bebenlebricolo/NanoFridgeThermostat/Hardware/Simulations/ACCurrentSensingAmp1.asc

C1: cap; 100n
C2: cap; 1µ
C3: cap; 1µ
C4: cap; 1µ
R1: res; 22k
R2: res; 10k
R3: res; 100k
R4: res; 56k
R5: res; 100k
R6: res; 100k
R7: res; 100k
R8: res; 10k
U1: TL072
U2: TL072
V1: signal; SINE(0 5m 50 0 0 0 2000)
V2: signal; SINE(0 2m 10000 0 0 0 2000)
V3: voltage; 5
Named nets: 0, VoutStage1, Filtered, Vin, Pol, Vcc, Vout
.tran 0 0.2 0
Dual stage TL072 JFet input op amp.
This configuration filters input AC current to select 50/60Hz main current
and feeds a 2 stages amplifier configuration.
Input amplitude (peak-to-peak) is around 5mV @50Hz
Output amplitude is about 180mV. 
Overall gain is around 36.
