bebenlebricolo/NanoFridgeThermostat/Firmware/src/Core/led.c

#include <stdbool.h>
#include <stddef.h>
#include <string.h>

#include "interpolation.h"
#include "led.h"

#ifdef LED_PWM_PULSE_STUFFING
#include "spanner.h"
#endif

typedef struct
{
    bool configured;           /**> Used to know if this specific LED construct is used or not      */
    led_io_t io;               /**> Static led IO config                                            */
    uint8_t io_state;          /**> IO state, only used for the LED_BLINK_NONE pattern (aka SOLID)  */
    mcu_time_t last_processed; /**> Last time this LED was processed (used to perform soft PWM)     */
    struct
    {
        led_blink_pattern_t current;  /**> Current LED Pattern (used to trigger state changed events)                                       */
        led_blink_pattern_t previous; /**> Previous LED Pattern (used to trigger state changed events)                                      */
    } patterns;

    led_next_event_t event; /**> Event that'll be triggered when the LED pattern is finished processing (some of the patterns have a limited life)  */

    struct
    {

        /**
         * @brief breathing LED pattern configuration and trackers
         */
        struct
        {
            uint16_t step;   /**> Keeps track of the current duty cycle applied to the LED   */
            bool new_step;   /**> Used to trigger the "new step" event. Some computation is performed only once to save time */
            uint8_t on_time; /**> Currently applied duty cycle : 0 - 100                                                     */

#ifdef LED_PWM_PULSE_STUFFING
            struct
            {
                bool used;     /**> Tells the algorithm whether stuffing is currently in use or not                   */
                uint8_t index; /**> Current index in the data sequence                                                */
                uint8_t sequence[LED_BLINK_BREATHING_RESOLUTION_MS]; /**> Sequence spans over max Resolution (for 100Hz signal with millisecond tick,
                                                                        resolution is 10). This field is used when the desired duty cycle can't be
                                                                        exactly represented with the physical resolution, hence pulse stuffing needs
                                                                        to be applied */

            } stuffing;
#endif /* LED_PWM_PULSE_STUFFING */
        } breathing;

        struct
        {
            uint8_t count; /**> Keeps track of the amount of blinks already executed       */
        } accept;
    } states;
} internal_config_t;

static internal_config_t internal_config[MAX_LED_COUNT];

static void handle_led_accept(mcu_time_t const *const time, internal_config_t *const config);
static void handle_led_warning(mcu_time_t const *const time, internal_config_t *const config);
static void handle_led_breathing(mcu_time_t const *const time, internal_config_t *const config);
static void get_elapsed_milliseconds(mcu_time_t const *const time, internal_config_t *const config, uint32_t *const elapsed);

static void led_on(led_io_t *const io);
static void led_set_io(led_io_t *const io, uint8_t state);
static void toggle_led(led_io_t *const io);
static void led_off(led_io_t *const io);

void led_static_config_default(led_io_t *io)
{
    io->pin = 0;
    io->port = NULL;
}

void led_reset(void)
{
    for (uint8_t i = 0; i < MAX_LED_COUNT; i++)
    {
        led_static_config_default(&internal_config[i].io);
        internal_config[i].configured = false;
        time_default(&internal_config[i].last_processed);
        internal_config[i].patterns.current = LED_BLINK_NONE;
        internal_config[i].patterns.previous = LED_BLINK_NONE;
        internal_config[i].event.kind = LED_NEXT_EVENT_NONE;
        internal_config[i].event.data.io_state = 0;
    }
}

void led_init(const led_io_t *config, const uint8_t length)
{
    led_reset();
    uint8_t max_length = length < MAX_LED_COUNT ? length : MAX_LED_COUNT;
    for (uint8_t i = 0; i < max_length; i++)
    {
        internal_config[i].io.port = config[i].port;
        internal_config[i].io.pin = config[i].pin;
        internal_config[i].configured = true;
        internal_config[i].states.breathing.step = 0;
        internal_config[i].states.breathing.new_step = true;

        // Pulse stuffing requires an additional data structure array
#ifdef LED_PWM_PULSE_STUFFING
        internal_config[i].states.breathing.stuffing.index = 0;
        internal_config[i].states.breathing.stuffing.used = false;
        memset(internal_config[i].states.breathing.stuffing.sequence, 0, LED_BLINK_BREATHING_RESOLUTION_MS);
#endif
    }
}

void led_set_blink_pattern(const uint8_t led_id, const led_blink_pattern_t pattern)
{
    if (led_id >= MAX_LED_COUNT)
    {
        return;
    }

    internal_config_t *config = &internal_config[led_id];
    config->patterns.current = pattern;

    // Reinitializes the "states" trackers
    switch (pattern)
    {
        case LED_BLINK_ACCEPT:
            config->states.accept.count = 0;
            break;

        case LED_BLINK_BREATHING:
            config->states.breathing.step = 0;
            // Forces the calculation of new values for the LED duty cycle (ms)
            config->states.breathing.new_step = true;
            break;

        case LED_BLINK_WARNING:
        default:
            break;
    }
}

void led_blink_none_set_io(const uint8_t led_id, const uint8_t io_state)
{
    internal_config_t *config = &internal_config[led_id];
    config->io_state = io_state;
}

void led_set_next_event(const uint8_t led_id, const led_next_event_t * event)
{
    if (led_id >= MAX_LED_COUNT)
    {
        return;
    }

    internal_config_t *config = &internal_config[led_id];
    config->event = *event;
}


void led_process(mcu_time_t const *const time)
{
    for (uint8_t i = 0; i < MAX_LED_COUNT; i++)
    {
        internal_config_t *const config = &internal_config[i];
        if (false == internal_config[i].configured)
        {
            // First non configured led implies there is no more configured ones after it
            // This is sufficient for us to jump out
            break;
        }

        // Update time of last processed (useful to start new patterns)
        if (config->patterns.current != config->patterns.previous)
        {
            config->last_processed = *time;
        }

        switch (config->patterns.current)
        {
            case LED_BLINK_BREATHING:
                handle_led_breathing(time, &internal_config[i]);
                break;

            case LED_BLINK_WARNING:
                handle_led_warning(time, &internal_config[i]);
                break;

            case LED_BLINK_ACCEPT:
                handle_led_accept(time, &internal_config[i]);
                break;

            case LED_BLINK_NONE:
            default:
                // Only turn the led off in case of event generation
                if (config->patterns.previous != config->patterns.current)
                {
                    if(0 == config->io_state)
                    {
                        led_off(&config->io);
                    }
                    else
                    {
                        led_on(&config->io);
                    }
                }

                break;
        }

        config->patterns.previous = config->patterns.current;
    }
}

static void handle_led_accept(mcu_time_t const *const time, internal_config_t *const config)
{
    uint32_t elapsed = 0;
    get_elapsed_milliseconds(time, config, &elapsed);

    if (elapsed >= LED_BLINK_ACCEPT_CYCLE_PERIOD_MS)
    {
        config->last_processed.milliseconds = time->milliseconds;
        config->states.accept.count++;
    }

    // Reverts back to original state when pattern is fully executed
    if (config->states.accept.count >= LED_BLINK_ACCEPT_FLASHES)
    {
        config->states.accept.count = 0;
        switch(config->event.kind)
        {
            case LED_NEXT_EVENT_IO_STATE:
                led_set_io(&config->io, config->event.data.io_state);
                config->patterns.current = LED_BLINK_NONE;
                break;

            case LED_NEXT_EVENT_PATTERN:
                config->patterns.current = config->event.data.pattern;
                break;

            default:
                config->patterns.current = LED_BLINK_NONE;
                break;
        }
        config->event.kind = LED_NEXT_EVENT_NONE;
        return;
    }

    uint32_t elapsed_clamped = elapsed % LED_BLINK_ACCEPT_CYCLE_PERIOD_MS;

    // First half of the cycle period (ON time)
    if (elapsed_clamped < LED_BLINK_ACCEPT_ON_TIME_MS)
    {
        led_on(&config->io);
    }
    // Second half of the cycle period (OFF time)
    else if (elapsed_clamped < LED_BLINK_ACCEPT_CYCLE_PERIOD_MS)
    {
        led_off(&config->io);
    }
}

static void handle_led_warning(mcu_time_t const *const time, internal_config_t *const config)
{
    uint32_t elapsed = (time->seconds - config->last_processed.seconds);
    if ((elapsed % LED_BLINK_WARNING_PERIOD_S) < LED_BLINK_WARNING_HALF_P)
    {
        led_on(&config->io);
    }
    else if ((elapsed % LED_BLINK_WARNING_PERIOD_S) < LED_BLINK_WARNING_PERIOD_S)
    {
        led_off(&config->io);
    }

    if (elapsed >= LED_BLINK_WARNING_PERIOD_S)
    {
        config->last_processed.seconds = time->seconds;
    }
}


uint8_t led_get_on_time_ticks(const uint8_t duty, const uint8_t resolution, const uint8_t duty_inc)
{
    range_uint8_t input = {.start = 0, .end = 100};
    range_uint8_t output = {.start = 0, .end = resolution};

    uint8_t on_time = interpolation_linear_uint8_to_uint8(duty, &input, &output);

    // This is to make sure that values like 95 - 99 will be represented as 100 instead of clamped to 90
    // Otherwise the LED is almost never at full brightness.
    // It also centers the range where the LED is at N% power :
    // duty     25  28  32  35  39  43 ... 91 95  98
    // led pow  30  30  30  40  40  40 ... 90 100 100

    // It's a form of rounding to the nearest decimal
    uint8_t remainder = (duty % duty_inc);
    if(remainder >= (duty_inc / 2U))
    {
        on_time++;
    }

    return on_time;
}

// Current performances (observed with an oscilloscope) :
// target frequency     25      50      75      100     150     200     225
// actual frequency     24.6    47.63   71.44   90.92   142.86  166.66  200,07
// % deviation          1%      4%       5%     9%      5%      16%     12%

static void handle_led_breathing(mcu_time_t const *const time, internal_config_t *config)
{
    static uint32_t elapsed = 0;
    get_elapsed_milliseconds(time, config, &elapsed);

    // Calculates new values for the currently evaluated step (only evaluated when we are running a new step)
    if (true == config->states.breathing.new_step)
    {
        uint8_t duty = led_breathing_get_duty_sawtooth(config->states.breathing.step);
        uint8_t on_time = led_get_on_time_ticks(duty, LED_BLINK_BREATHING_RESOLUTION_MS, LED_BLINK_BREATHING_DUTY_INCREMENT_PER_RESOLUTION_POINT);

        config->states.breathing.on_time = on_time;
        config->states.breathing.new_step = false;

#ifdef LED_PWM_PULSE_STUFFING
        if (on_time / LED_BLINK_BREATHING_RESOLUTION_MS != config->states.breathing.on_time / LED_BLINK_BREATHING_RESOLUTION_MS)
        {
            // Only recompute if we are moving to a new multiple (e.g. 3x to 4x)
            uint8_t remainder = duty % LED_BLINK_BREATHING_RESOLUTION_MS;
            if (remainder == 0)
            {
                // We can represent exactly the duty cycle with the current resolution
                // Se we're good to go without using the stuffing method.
                config->states.breathing.stuffing.used = false;
            }
            else
            {
                config->states.breathing.stuffing.used = true;
                config->states.breathing.stuffing.index = 0;
                span_data_t data = {.a_val = duty / LED_BLINK_BREATHING_RESOLUTION_MS,
                                    .b_val = duty / LED_BLINK_BREATHING_RESOLUTION_MS + 1,
                                    .a_cnt = (LED_BLINK_BREATHING_RESOLUTION_MS - remainder),
                                    .b_cnt = remainder};
                span(&data, config->states.breathing.stuffing.sequence, LED_BLINK_BREATHING_RESOLUTION_MS);
            }
        }
#endif /* LED_PWM_PULSE_STUFFING */
    }

    // Time to process the new duty-cycle
    // Event is generated at a target frequency of 25Hz
    if (elapsed <= LED_BLINK_BREATHING_RESOLUTION_MS)
    {

#ifdef LED_PWM_PULSE_STUFFING
        if (true == config->states.breathing.stuffing.used)
        {
            uint8_t index = config->states.breathing.stuffing.index;
            config->states.breathing.on_time = config->states.breathing.stuffing.sequence[index];
        }
#endif /* LED_PWM_PULSE_STUFFING */

        if (config->states.breathing.on_time == 0)
        {
            led_off(&config->io);
            return;
        }

        if (config->states.breathing.on_time == LED_BLINK_BREATHING_RESOLUTION_MS)
        {
            led_on(&config->io);
            return;
        }

        if (elapsed < config->states.breathing.on_time)
        {
            led_on(&config->io);
        }
        else
        {
            // Switch off the LED
            led_off(&config->io);
        }
    }
    // Reset the window
    else
    {
        config->last_processed = *time;
        config->states.breathing.step++;
        config->states.breathing.new_step = true;
        config->states.breathing.step %= LED_BLINK_BREATHING_FULL_CYCLE_STEPS;

#ifdef LED_PWM_PULSE_STUFFING
        if (config->states.breathing.stuffing.index < (LED_BLINK_BREATHING_RESOLUTION_MS - 1))
        {
            // Prevent recomputing
            config->states.breathing.stuffing.index++;
            // config->states.breathing.new_step = false;
        }
        else
        {
            config->states.breathing.stuffing.index = 0;
        }
#endif /* LED_PWM_PULSE_STUFFING */
    }
}

static void led_on(led_io_t *const io)
{
    *io->port |= (1 << io->pin);
}

static void led_set_io(led_io_t *const io, uint8_t state)
{
    if(state != 0)
    {
        led_on(io);
    }
    else
    {
        led_off(io);
    }
}


// static void toggle_led(led_io_t *const io)
// {
//     *io->port ^= (1 << io->pin);
// }


static void led_off(led_io_t *const io)
{
    *io->port &= ~(1 << io->pin);
}

static void get_elapsed_milliseconds(mcu_time_t const *const time, internal_config_t *const config, uint32_t *const elapsed)
{
    if (time->milliseconds >= config->last_processed.milliseconds)
    {
        *elapsed = time->milliseconds - config->last_processed.milliseconds;
    }
    // Milliseconds was reset to 0 after reaching 1000
    else
    {
        *elapsed = (time->milliseconds + 1000) - config->last_processed.milliseconds;
    }
}

uint8_t led_breathing_get_duty_sawtooth(const uint16_t step)
{
    uint16_t duty = 0;
    // Sawtooth implementation, positive ramp (0 to 100)
    if (step < LED_BLINK_BREATHING_HALF_CYCLE_STEPS)
    {
        duty = (step * LED_BLINK_BREATHING_DUTY_CYCLE_INC) / (LED_BLINK_BREATHING_DUTY_CYCLE_INC_ALIASING_FACTOR);
    }
    // Sawtooth implementation, negative ramp (100 to 0)
    else
    {
        duty = ((step - (LED_BLINK_BREATHING_HALF_CYCLE_STEPS)) * LED_BLINK_BREATHING_DUTY_CYCLE_INC);
        duty /= LED_BLINK_BREATHING_DUTY_CYCLE_INC_ALIASING_FACTOR;
        duty = 100 - duty;
    }

    return (uint8_t)duty;
}
