bebenlebricolo/NanoFridgeThermostat/Firmware/src/Core/bridge.c

#include "bridge.h"

void bridge_get_lower_resistance(uint16_t const * const upper_resistance, uint16_t const * const voltage_mv, uint16_t const * const vcc_mv, uint16_t * out_resistance)
{
    // Can't divide by 0, this is an error case
    if(*vcc_mv == *voltage_mv)
    {
        *out_resistance = UINT16_MAX;
        return;
    }

    uint32_t delta_t = *vcc_mv - *voltage_mv;
    uint32_t numerator = ((uint32_t) *upper_resistance) * ( (uint32_t) *voltage_mv);
    *out_resistance = (uint16_t) (numerator / delta_t);
}
