bebenlebricolo/NanoFridgeThermostat/Firmware/src/Core/buttons.c

#include "buttons.h"

#define LOW 0U
#define HIGH 1U

void button_local_mem_default(button_local_mem_t *button)
{
    button->current = LOW;
    button->previous = LOW;
    button->pressed = 0;
    button->event = BUTTON_STATE_DEFAULT;
}

void read_single_button_event(button_local_mem_t *const button, uint32_t const *const time)
{
    if (button->current == LOW)
    {
        // Start of long press, count press duration
        if (button->current == button->previous)
        {
            const uint32_t duration = *time - button->pressed;
            if (duration >= BUTTON_PRESS_TIME_THRESHOLD)
            {
                button->event = BUTTON_STATE_HOLD;
            }
        }
        // New button pressed event (was not pressed before)
        else
        {
            button->event = BUTTON_STATE_PRESSED;
            button->pressed = *time;
        }
    }
    // Button is released
    else
    {
        button->event = BUTTON_STATE_RELEASED;
    }
    button->previous = button->current;
}
