bebenlebricolo/NanoFridgeThermostat/Firmware/src/Core/thermistor_ntc_100k_3950K.h

#ifndef THERMISTOR_NTC_100K_3950K_HEADER
#define THERMISTOR_NTC_100K_3950K_HEADER

#ifdef __cplusplus
extern "C" {
#endif

#include "thermistor.h"

#define THERMISTOR_NTC_100K_3950K_SAMPLE_COUNT 23U

extern const thermistor_data_t thermistor_ntc_100k_3950K_data;

#ifdef __cplusplus
}
#endif

#endif /* THERMISTOR_NTC_100K_3950K_HEADER */
